HwzLoveDz/AXP202-PMIC/software/ESP-IDF/PMU_AXP20x/main/i2c_port.c

#include "i2c_port.h"

/**
 * @brief i2c master initialization
 */
esp_err_t i2c_master_init(void)
{
    int i2c_master_port = I2C_MASTER_NUM;
    static i2c_config_t conf;   //! i2c_config_t conf;
    /* 
     * 报错原因：因为 conf 是函数内的局部变量，导致 conf 有成员未初始化，会从 stack 里分配内存空间，值未知
     * 解决方法：将 conf 声明为静态局部变量解决
     */
    conf.mode = I2C_MODE_MASTER;
    conf.sda_io_num = I2C_MASTER_SDA_IO;
    conf.sda_pullup_en = GPIO_PULLUP_ENABLE;
    conf.scl_io_num = I2C_MASTER_SCL_IO;
    conf.scl_pullup_en = GPIO_PULLUP_ENABLE;
    conf.master.clk_speed = I2C_MASTER_FREQ_HZ;
    i2c_param_config(i2c_master_port, &conf);
    return i2c_driver_install(i2c_master_port, conf.mode, I2C_MASTER_RX_BUF_DISABLE, I2C_MASTER_TX_BUF_DISABLE, 0);
}

/**
 * @brief apx library i2c read callback
 * 
 */
uint32_t twi_read(uint8_t dev_addr, uint8_t reg_addr, uint8_t *data, uint8_t len)   //! 类型错误：uint16_t
{
    if (len == 0) {
        return ESP_OK;
    }
    if (data == NULL) {
        return ESP_FAIL;
    }
    i2c_cmd_handle_t cmd;

    cmd = i2c_cmd_link_create();
    i2c_master_start(cmd);
    i2c_master_write_byte(cmd, (dev_addr << 1) | WRITE_BIT, ACK_CHECK_EN);
    i2c_master_write_byte(cmd, reg_addr, ACK_CHECK_EN);
    i2c_master_stop(cmd);
    esp_err_t ret =  i2c_master_cmd_begin(I2C_MASTER_NUM, cmd, 1000 / portTICK_PERIOD_MS);
    i2c_cmd_link_delete(cmd);
    if (ret != ESP_OK) {
        return ESP_FAIL;
    }
    cmd = i2c_cmd_link_create();
    i2c_master_start(cmd);
    i2c_master_write_byte(cmd, (dev_addr << 1) | READ_BIT, ACK_CHECK_EN);
    if (len > 1) {
        i2c_master_read(cmd, data, len - 1, ACK_VAL);
    }
    i2c_master_read_byte(cmd, &data[len - 1], NACK_VAL);
    i2c_master_stop(cmd);
    ret = i2c_master_cmd_begin(I2C_MASTER_NUM, cmd, 1000 / portTICK_PERIOD_MS);
    i2c_cmd_link_delete(cmd);
    return ret;
}

/**
 * @brief apx library i2c write callback
 */
uint32_t twi_write(uint8_t dev_addr, uint8_t reg_addr, uint8_t *data, uint8_t len)  //! 类型错误：uint16_t
{
    if (data == NULL) {
        return ESP_FAIL;
    }
    i2c_cmd_handle_t cmd = i2c_cmd_link_create();
    i2c_master_start(cmd);
    i2c_master_write_byte(cmd, (dev_addr << 1) | WRITE_BIT, ACK_CHECK_EN);
    i2c_master_write_byte(cmd, reg_addr, ACK_CHECK_EN);
    i2c_master_write(cmd, data, len, ACK_CHECK_EN);
    i2c_master_stop(cmd);
    esp_err_t ret = i2c_master_cmd_begin(I2C_MASTER_NUM, cmd, 1000 / portTICK_PERIOD_MS);
    i2c_cmd_link_delete(cmd);
    return ret;
}
