HwzLoveDz/AXP202-PMIC/software/Arduino/AXP202X/examples/axp_base/axp_base.ino

/*
MIT License

Copyright (c) 2019 lewis he

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
THE SOFTWARE IS PROVIDED "AS IS", WITHOUT WARRANTY OF ANY KIND, EXPRESS OR
IMPLIED, INCLUDING BUT NOT LIMITED TO THE WARRANTIES OF MERCHANTABILITY,
FITNESS FOR A PARTICULAR PURPOSE AND NONINFRINGEMENT. IN NO EVENT SHALL THE
AUTHORS OR COPYRIGHT HOLDERS BE LIABLE FOR ANY CLAIM, DAMAGES OR OTHER
LIABILITY, WHETHER IN AN ACTION OF CONTRACT, TORT OR OTHERWISE, ARISING FROM,
OUT OF OR IN CONNECTION WITH THE SOFTWARE OR THE USE OR OTHER DEALINGS IN THE
SOFTWARE.
*/
#include <Wire.h>
#include <axp20x.h>

// AXP20X_Class axp;
bool  axpIrq = 0;

const uint8_t i2c_sda = 21;
const uint8_t i2c_scl = 22;
const uint8_t axp_irq_pin = 35;

void setFlag(void)
{
    axpIrq = true;
}

void setup()
{
    Serial.begin(115200);
    Wire.begin(i2c_sda, i2c_scl);

    //! Use the Wire port
    int ret = axp.begin(Wire, AXP192_SLAVE_ADDRESS);
    // int ret = axp.begin(Wire);
    if (ret == AXP_FAIL) {
        Serial.println("AXP Power begin failed");
        while (1);
    }

    Serial.println();
    axp.setVWarningLevel1(3450);
    axp.setVWarningLevel2(3400);
    uint16_t level1 = axp.getVWarningLevel1();
    uint16_t level2 = axp.getVWarningLevel2();
    Serial.printf("getVWarningLevel1:%u mV \n", level1 );
    Serial.printf("getVWarningLevel2:%u mV \n", level2);
    Serial.printf("getPowerDonwVoltage:%u mV \n", axp.getPowerDownVoltage());
    axp.setPowerDownVoltage(2600);
    Serial.printf("getPowerDonwVoltage:%u mV \n", axp.getPowerDownVoltage());
    Serial.println();

    //! attachInterrupt to gpio 35
    pinMode(axp_irq_pin, INPUT_PULLUP);
    attachInterrupt(axp_irq_pin, setFlag, FALLING);
    axp.clearIRQ();

    //! enable all irq channel
    axp.enableIRQ(AXP202_ALL_IRQ, true);

    axp.setPowerOutPut(AXP202_DCDC3, AXP202_ON);
    axp.setPowerOutPut(AXP202_EXTEN, AXP202_ON);
    axp.setPowerOutPut(AXP202_LDO2,  AXP202_ON);
    axp.setPowerOutPut(AXP202_LDO4,  AXP202_ON);
    axp.setPowerOutPut(AXP202_DCDC2, AXP202_ON);
    axp.setLDO4Voltage(AXP202_LDO4_3300MV);
    axp.setLDO3Voltage(3500);
    axp.setPowerOutPut(AXP202_LDO3, AXP202_ON);

    Serial.print("DC2:");
    Serial.print(axp.isDCDC2Enable() ? String(axp.getDCDC2Voltage()) + " mv" : "DISABLE");
    Serial.print("  ");

    Serial.print("DC3:");
    Serial.print(axp.isDCDC3Enable() ? String(axp.getDCDC3Voltage()) + " mv" : "DISABLE");
    Serial.print("  ");

    Serial.print("LDO2:");
    Serial.print(axp.isLDO2Enable() ? String(axp.getLDO2Voltage()) + " mv" : "DISABLE");
    Serial.print("  ");

    Serial.print("LDO3:");
    Serial.print(axp.isLDO3Enable() ? String(axp.getLDO3Voltage()) + " mv" : "DISABLE");
    Serial.print("  ");

    Serial.print("LDO4:");
    Serial.print(axp.isLDO4Enable() ? "ENABLE" : "DISABLE");
    Serial.print("  ");

    Serial.print("Exten:");
    Serial.print(axp.isExtenEnable() ? "ENABLE" : "DISABLE");
    Serial.print("\r\n");

    axp.setTimer(1);
}


void loop()
{
    if (axpIrq) {
        axpIrq = 0;
        axp.readIRQ();
        Serial.println("axp20x irq enter!");
        if (axp.isAcinOverVoltageIRQ()) {
            Serial.printf("isAcinOverVoltageIRQ\n");
        }
        if (axp.isAcinPlugInIRQ()) {
            Serial.printf("isAcinPlugInIRQ\n");
        }
        if (axp.isAcinRemoveIRQ()) {
            Serial.printf("isAcinRemoveIRQ\n");
        }
        if (axp.isVbusOverVoltageIRQ()) {
            Serial.printf("isVbusOverVoltageIRQ\n");
        }
        if (axp.isVbusPlugInIRQ()) {
            Serial.printf("isVbusPlugInIRQ\n");
        }
        if (axp.isVbusRemoveIRQ()) {
            Serial.printf("isVbusRemoveIRQ\n");
        }
        if (axp.isVbusLowVHOLDIRQ()) {
            Serial.printf("isVbusLowVHOLDIRQ\n");
        }
        if (axp.isBattPlugInIRQ()) {
            Serial.printf("isBattPlugInIRQ\n");
        }
        if (axp.isBattRemoveIRQ()) {
            Serial.printf("isBattRemoveIRQ\n");
        }
        if (axp.isBattEnterActivateIRQ()) {
            Serial.printf("isBattEnterActivateIRQ\n");
        }
        if (axp.isBattExitActivateIRQ()) {
            Serial.printf("isBattExitActivateIRQ\n");
        }
        if (axp.isChargingIRQ()) {
            Serial.printf("isChargingIRQ\n");
        }
        if (axp.isChargingDoneIRQ()) {
            Serial.printf("isChargingDoneIRQ\n");
        }
        if (axp.isBattTempLowIRQ()) {
            Serial.printf("isBattTempLowIRQ\n");
        }
        if (axp.isBattTempHighIRQ()) {
            Serial.printf("isBattTempHighIRQ\n");
        }
        if (axp.isChipOvertemperatureIRQ()) {
            Serial.printf("isChipOvertemperatureIRQ\n");
        }
        if (axp.isChargingCurrentLessIRQ()) {
            Serial.printf("isChargingCurrentLessIRQ\n");
        }
        if (axp.isDC2VoltageLessIRQ()) {
            Serial.printf("isDC2VoltageLessIRQ\n");
        }
        if (axp.isDC3VoltageLessIRQ()) {
            Serial.printf("isDC3VoltageLessIRQ\n");
        }
        if (axp.isLDO3VoltageLessIRQ()) {
            Serial.printf("isLDO3VoltageLessIRQ\n");
        }
        if (axp.isPEKShortPressIRQ()) {
            Serial.printf("isPEKShortPressIRQ\n");
        }
        if (axp.isPEKLongtPressIRQ()) {
            Serial.printf("isPEKLongtPressIRQ\n");
        }
        if (axp.isNOEPowerOnIRQ()) {
            Serial.printf("isNOEPowerOnIRQ\n");
        }
        if (axp.isNOEPowerDownIRQ()) {
            Serial.printf("isNOEPowerDownIRQ\n");
        }
        if (axp.isVBUSEffectiveIRQ()) {
            Serial.printf("isVBUSEffectiveIRQ\n");
        }
        if (axp.isVBUSInvalidIRQ()) {
            Serial.printf("isVBUSInvalidIRQ\n");
        }
        if (axp.isVUBSSessionIRQ()) {
            Serial.printf("isVUBSSessionIRQ\n");
        }
        if (axp.isVUBSSessionEndIRQ()) {
            Serial.printf("isVUBSSessionEndIRQ\n");
        }
        if (axp.isLowVoltageLevel1IRQ()) {
            Serial.printf("isLowVoltageLevel1IRQ\n");
        }
        if (axp.isLowVoltageLevel2IRQ()) {
            Serial.printf("isLowVoltageLevel2IRQ\n");
        }
        if (axp.isTimerTimeoutIRQ()) {
            Serial.printf("isTimerTimeoutIRQ\n");
            axp.offTimer();
            axp.setChgLEDMode(AXP20X_LED_BLINK_1HZ);
        }
        if (axp.isPEKRisingEdgeIRQ()) {
            Serial.printf("isPEKRisingEdgeIRQ\n");
        }
        if (axp.isPEKFallingEdgeIRQ()) {
            Serial.printf("isPEKFallingEdgeIRQ\n");
        }
        if (axp.isGPIO3InputEdgeTriggerIRQ()) {
            Serial.printf("isGPIO3InputEdgeTriggerIRQ\n");
        }
        if (axp.isGPIO2InputEdgeTriggerIRQ()) {
            Serial.printf("isGPIO2InputEdgeTriggerIRQ\n");
        }
        if (axp.isGPIO1InputEdgeTriggerIRQ()) {
            Serial.printf("isGPIO1InputEdgeTriggerIRQ\n");
        }
        if (axp.isGPIO0InputEdgeTriggerIRQ()) {
            Serial.printf("isGPIO0InputEdgeTriggerIRQ\n");
        }
        axp.clearIRQ();
    }
}
